J0NTrollston/Handheld-Compass-MC/Code/Handheld_Compass_MC/src/LED.cpp

/*--------------------------------------------------------------------
Name:   Brandon Ramos
Date:   7/26/2025
File:   LED functions

Doc:  Below is the LED array where 21 is the center 

->       [38] [39] [40] [41] [42] [43] [44] [45] [46]
    [37] [36] [35] [34] [33] [32] [31] [30] [29] [28] [27]  <-
->  [16] [17] [18] [19] [20] [21] [22] [23] [24] [25] [26]
    [15] [14] [13] [12] [11] [10] [09] [08] [07] [06]       <-
->            [00] [01] [02] [03] [04] [05]
--------------------------------------------------------------------*/
#include <FastLED.h>
#include "LED.h"

// How many leds in your strip?
#define NUM_LEDS 47

// For led chips like WS2812, which have a data line, ground, and power, you just
// need to define DATA_PIN. 
#define DATA_PIN 7
#define COLOR_ORDER  GRB //Is GRB but can also be RGB

// Define the array of leds
CRGB leds[NUM_LEDS];

/******************************************************** 
* Setup to describe the model, pin and color for the led array
********************************************************/
void setupLED(){
    FastLED.addLeds<WS2812, DATA_PIN, COLOR_ORDER>(leds, NUM_LEDS);  // GRB ordering is typical
}

/******************************************************** 
* Test all LEDs one at a time 
* Test the Compass Head pointing up
********************************************************/
void testLED(){
  // Turn the LED on, then pause
  for(int i = 0; i<NUM_LEDS; i++){
    // Test LED
    leds[i] = CRGB::Green;
    // Turn the previous LED off. If i starts over then turn the last LED off.
    if(i == 0 ){
      leds[NUM_LEDS-1] = CRGB::Black;
    }else{
      leds[i-1] = CRGB::Black;
    }
  }
}

/******************************************************** 
* Turn off LEDs before displaying next direction
********************************************************/
static void turnOffAllLEDS(){
  for(int i = 0; i < NUM_LEDS; i++){
    leds[i] = CRGB::Black;
  }
}

/******************************************************** 
* Given a heading from 0-360 degrees, display the LED array to show north
********************************************************/
void compassHead(float heading){

  if((360-heading) > 349.0 or (360-heading) <= 191.0){
    /*
     Reason for taking the difference in 360 degrees and the heading is to 
     account for how I measured the compass heading. I measured the angle of 
     the compass head to where it was pointing in reference to the top of the 
     compass being 0,360 degrees. Because of this, when you actually use it 
     you will need to offset by taking (360-heading) to display magnetic north.     
  */
    heading = 360 - heading;

    // If pointing North
    //  xxxxRxxxx    
    // xxxxxRxxxxx   
    // xxxxGRGxxxx   
    // xxxxxGxxxxX   
    //  XxxxxxxXX 
    if(heading > 349.0 or heading <= 11.6){

        //Turn off all LEDs
        turnOffAllLEDS();

        leds[42] = CRGB::Red;

        leds[32] = CRGB::Red;

        leds[20] = CRGB::Gray;
        leds[21] = CRGB::Red;
        leds[22] = CRGB::Gray;

        leds[10] = CRGB::Gray;
        
        FastLED.show();
    }

    // Step 1
    //  xxxxRRxxx    
    // xxxxxRxxxxx   
    // xxxxGRGxxxx   
    // xxxxxGxxxxX   
    //  XxxxxxxXX 
    else if(heading > 11.6 and heading <= 18.9){

        //Turn off all LEDs
        turnOffAllLEDS();

        leds[42] = CRGB::Red;
        leds[43] = CRGB::Red;

        leds[32] = CRGB::Red;

        leds[20] = CRGB::Gray;
        leds[21] = CRGB::Red;
        leds[22] = CRGB::Gray;

        leds[10] = CRGB::Gray;

        FastLED.show();
    }

    // Step 2
    //  xxxxxRxxx    
    // xxxxxRxxxxx   
    // xxxxGRGxxxx   
    // xxxxxGxxxxX   
    //  XxxxxxxXX 
    else if(heading > 18.9 and heading <= 19.1){

        //Turn off all LEDs
        turnOffAllLEDS();

        leds[43] = CRGB::Red;

        leds[32] = CRGB::Red;

        leds[20] = CRGB::Gray;
        leds[21] = CRGB::Red;
        leds[22] = CRGB::Gray;

        leds[10] = CRGB::Gray;

        FastLED.show();
    }

    // Step 3
    //  xxxxxRxxx    
    // xxxxxRRxxxx   
    // xxxxGRGxxxx   
    // xxxxxGxxxxX   
    //  XxxxxxxXX 
    else if(heading > 19.1 and heading <= 20.6){

        //Turn off all LEDs
        turnOffAllLEDS();

        leds[43] = CRGB::Red;

        leds[32] = CRGB::Red;
        leds[31] = CRGB::Red;

        leds[20] = CRGB::Gray;
        leds[21] = CRGB::Red;
        leds[22] = CRGB::Gray;

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
        leds[11] = CRGB::Red;
        
        leds[2] = CRGB::Red;

        FastLED.show();
    }

    // Step -43
    //  xxxxxxxxx    
    // xxxxxGxxxxx   
    // xxxxGRGxxxx   
    // xxxxRRxxxxX   
    //  XxxRxxxXX 
    else if(heading > 155.1 and heading <= 160.9){

        //Turn off all LEDs
        turnOffAllLEDS();

        leds[32] = CRGB::Gray;

        leds[20] = CRGB::Gray;
        leds[21] = CRGB::Red;
        leds[22] = CRGB::Gray;
        
        leds[10] = CRGB::Red;
        leds[11] = CRGB::Red;
        
        leds[2] = CRGB::Red;

        FastLED.show();
    }

    // Step -44
    //  xxxxxxxxx    
    // xxxxxGxxxxx   
    // xxxxGRGxxxx   
    // xxxxxRxxxxX   
    //  XxxRxxxXX 
    else if(heading > 160.9 and heading <= 161.1){

        //Turn off all LEDs
        turnOffAllLEDS();

        leds[32] = CRGB::Gray;

        leds[20] = CRGB::Gray;
        leds[21] = CRGB::Red;
        leds[22] = CRGB::Gray;
        
        leds[10] = CRGB::Red;
        
        leds[2] = CRGB::Red;

        FastLED.show();
    }

    // Step -45
    //  xxxxxxxxx    
    // xxxxxGxxxxx   
    // xxxxGRGxxxx   
    // xxxxxRxxxxX   
    //  XxxRRxxXX 
    else if(heading > 161.1 and heading <= 168.4){

        //Turn off all LEDs
        turnOffAllLEDS();

        leds[32] = CRGB::Gray;

        leds[20] = CRGB::Gray;
        leds[21] = CRGB::Red;
        leds[22] = CRGB::Gray;
        
        leds[10] = CRGB::Red;
        
        leds[2] = CRGB::Red;
        leds[3] = CRGB::Red;

        FastLED.show();
    }else {
        turnOffAllLEDS();
    }
  }
}
